atomic14/voice-controlled-robot/firmware/src/CommandProcessor.cpp

#include <Arduino.h>
#include "CommandProcessor.h"

const char *words[] = {
    "forward",
    "backward",
    "left",
    "right",
    "_nonsense",
};

void commandQueueProcessorTask(void *param)
{
    CommandProcessor *commandProcessor = (CommandProcessor *)param;
    while (true)
    {
        uint16_t commandIndex = 0;
        if (xQueueReceive(commandProcessor->m_command_queue_handle, &commandIndex, portMAX_DELAY) == pdTRUE)
        {
            commandProcessor->processCommand(commandIndex);
        }
    }
}

int calcDuty(int ms)
{
    // 50Hz = 20ms period
    return (65536 * ms) / 20000;
}

const int leftForward = 1600;
const int leftBackward = 1400;
const int leftStop = 1500;
const int rightBackward = 1600;
const int rightForward = 1445;
const int rightStop = 1500;

void CommandProcessor::processCommand(uint16_t commandIndex)
{
    digitalWrite(GPIO_NUM_2, HIGH);
    switch (commandIndex)
    {
    case 0: // forward
        ledcWrite(0, calcDuty(leftForward));
        ledcWrite(1, calcDuty(rightForward));
        vTaskDelay(1000 / portTICK_PERIOD_MS);
        break;
    case 1: // backward
        ledcWrite(0, calcDuty(leftBackward));
        ledcWrite(1, calcDuty(rightBackward));
        vTaskDelay(1000 / portTICK_PERIOD_MS);
        break;
    case 2: // left
        ledcWrite(0, calcDuty(leftBackward));
        ledcWrite(1, calcDuty(rightForward));
        vTaskDelay(500 / portTICK_PERIOD_MS);
        break;
    case 3: // right
        ledcWrite(0, calcDuty(leftForward));
        ledcWrite(1, calcDuty(rightBackward));
        vTaskDelay(500 / portTICK_PERIOD_MS);
        break;
    }
    digitalWrite(GPIO_NUM_2, LOW);
    ledcWrite(0, calcDuty(leftStop));  // stop
    ledcWrite(1, calcDuty(rightStop)); // stop
}

CommandProcessor::CommandProcessor()
{
    pinMode(GPIO_NUM_2, OUTPUT);
    // setup the motors
    ledcSetup(0, 50, 16);
    ledcAttachPin(GPIO_NUM_13, 0);
    ledcSetup(1, 50, 16);
    ledcAttachPin(GPIO_NUM_12, 1);
    ledcWrite(0, calcDuty(1500)); // left
    ledcWrite(1, calcDuty(1500)); // right

    // allow up to 5 commands to be in flight at once
    m_command_queue_handle = xQueueCreate(5, sizeof(uint16_t));
    if (!m_command_queue_handle)
    {
        Serial.println("Failed to create command queue");
    }
    // kick off the command processor task
    TaskHandle_t command_queue_task_handle;
    xTaskCreate(commandQueueProcessorTask, "Command Queue Processor", 1024, this, 1, &command_queue_task_handle);
}

void CommandProcessor::queueCommand(uint16_t commandIndex, float best_score)
{
    // unsigned long now = millis();
    if (commandIndex != 5 && commandIndex != -1)
    {
        Serial.printf("***** %ld Detected command %s(%f)\n", millis(), words[commandIndex], best_score);
        if (xQueueSendToBack(m_command_queue_handle, &commandIndex, 0) != pdTRUE)
        {
            Serial.println("No more space for command");
        }
    }
}
